chengkun-yang/ece-445l-lab-6-chengkun-yang/Resources/Lab 10/call_graph.png

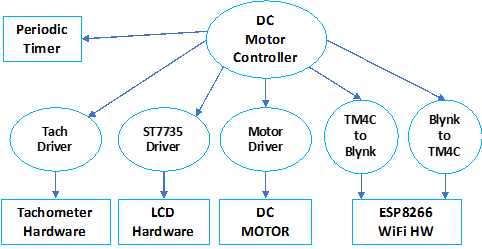
Resources/Lab 10/call_graph.png
