chengkun-yang/ece-445l-lab-6-chengkun-yang/Resources/Lab 10/figure_10.13.png

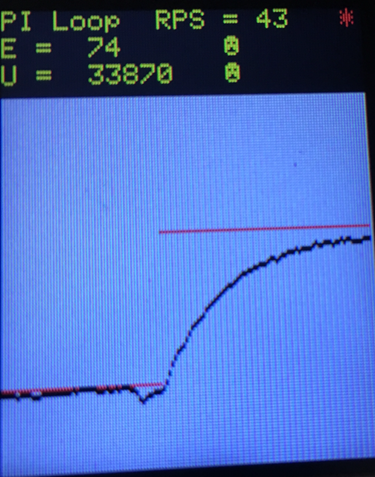
Resources/Lab 10/figure_10.13.png
