chengkun-yang/ece-445l-lab-6-chengkun-yang/Resources/Lab 10/figure_10.15.png

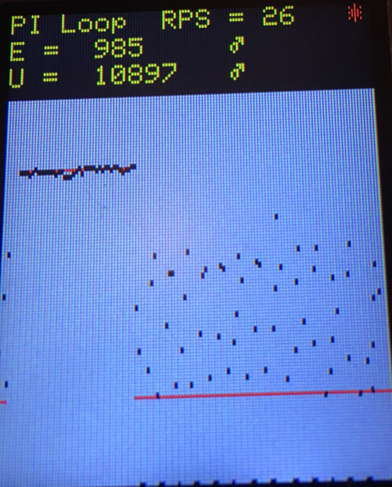
Resources/Lab 10/figure_10.15.png
