chengkun-yang/ece-445l-lab-6-chengkun-yang/Resources/Lab 10/lab_10_block_diagram.png

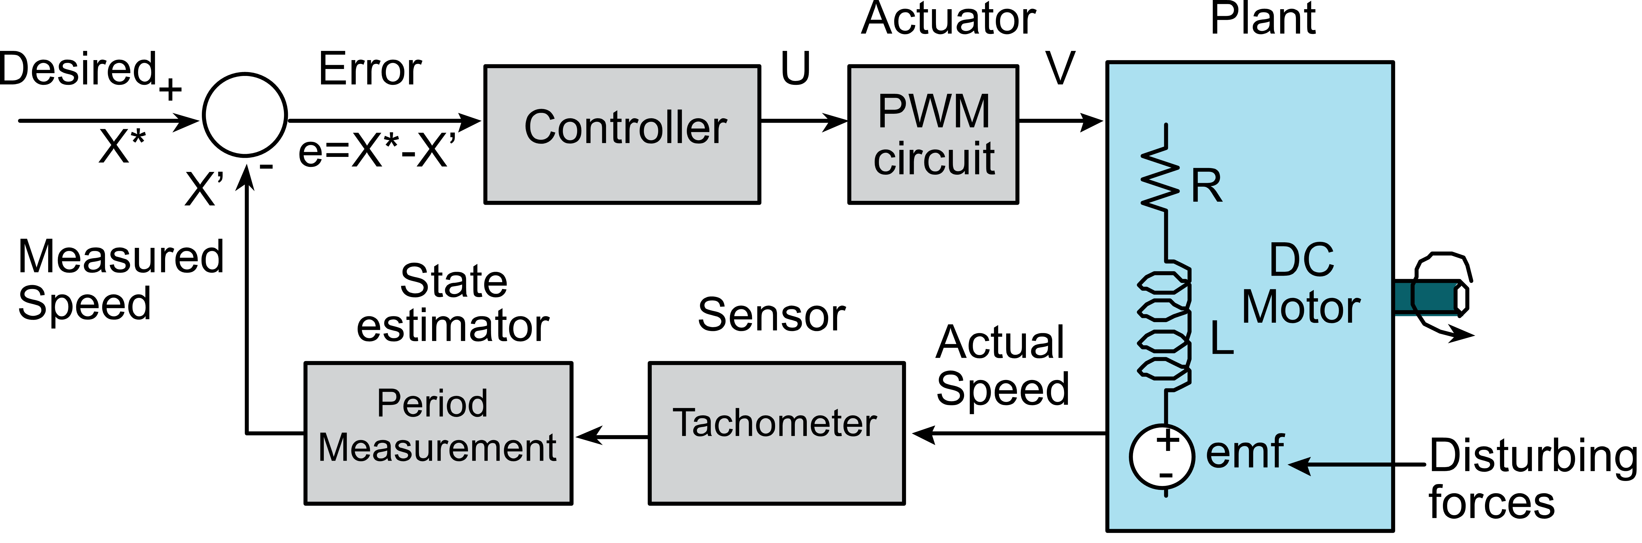
Resources/Lab 10/lab_10_block_diagram.png
